nbxmike/PSOC-Console/PSOC-Creator/Composite-HID.cydsn/LEDsOut.c

/* ========================================
 *
 * Copyright 2021 Michael McCormack
 *
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
 * ========================================
*/

#include <project.h>
#include "FreeRTOS.h"
#include "timers.h"
#include "LEDsOut.h"


#define LEDSOUT_SLOW_ON           (0)
#define LEDSOUT_SLOW_OFF          (1)

#define LEDOUTPUT_ON              (1)
#define LEDOUTPUT_OFF             (0)

#define LEDSOUT_FAST_ON           (0)
#define LEDSOUT_FAST_OFF          (1)
#define LEDSOUT_DOUBLE_ONE_ON     (0)
#define LEDSOUT_DOUBLE_ONE_OFF    (1)
#define LEDSOUT_DOUBLE_TWO_ON     (2)
#define LEDSOUT_DOUBLE_TWO_OFF    (3)
#define LEDSOUT_DOUBLE_PAUSE      (4)
#define LEDSOUT_TRIPLE_ONE_ON     (0)
#define LEDSOUT_TRIPLE_ONE_OFF    (1)
#define LEDSOUT_TRIPLE_TWO_ON     (2)
#define LEDSOUT_TRIPLE_TWO_OFF    (3)
#define LEDSOUT_TRIPLE_THREE_ON   (4)
#define LEDSOUT_TRIPLE_THREE_OFF  (5)
#define LEDSOUT_TRIPLE_PAUSE      (6)
#define LEDSOUT_DASH_ON           (0)
#define LEDSOUT_DASH_OFF          (1)
#define LEDSOUT_DOT_ON            (2)
#define LEDSOUT_DOT_OFF           (3)

static LED_Output_t Leds[LEDSOUT_COUNT];
static TickType_t xLastTransactionTime;
static const uint8_t AndMasks[8] =  {0xFE, 0xFD, 0xFB, 0xF7, 0xEF, 0xDF, 0xBF, 0x7F};
static const uint8_t OrMasks[8] =  {0x01, 0x02, 0x04, 0x08, 0x10, 0x20, 0x40, 0x80};

void LEDSOut_Task(void *arg);

static int LEDsOut_Off(LED_Output_t *Led);
static int LEDsOut_SteadyOn(LED_Output_t *Led);
static int LEDsOut_Slow(LED_Output_t *Led);
static int LEDsOut_Fast(LED_Output_t *Led);
static int LEDsOut_Double(LED_Output_t *Led);
static int LEDsOut_Triple(LED_Output_t *Led);
static int LEDsOut_DashDot(LED_Output_t *Led);


int (*state_function[LEDSOUT_MODE_INVALID]) (LED_Output_t *Led) = {
    LEDsOut_Off,
    LEDsOut_SteadyOn,
    LEDsOut_Slow,
    LEDsOut_Fast,
    LEDsOut_Double,
    LEDsOut_Triple,
    LEDsOut_DashDot
};

static int LEDsOut_Off(LED_Output_t *Led)
{
    Led->onOff = LEDOUTPUT_OFF;
    return Led->onOff;
}

static int LEDsOut_SteadyOn(LED_Output_t *Led)
{
    Led->onOff = LEDOUTPUT_ON;
    return Led->onOff;
}


static int LEDsOut_Slow(LED_Output_t *Led)
{
    switch (Led->state)
    {
        case LEDSOUT_SLOW_ON:
            Led->onOff = LEDOUTPUT_ON;
            Led->count = Led->count + LEDSOUT_RATE_TICK;
            if (Led->count >= LEDSOUT_RATE_SLOW)
            {
                Led->state = LEDSOUT_SLOW_OFF;
                Led->count = 0;
            }
            break;
        case LEDSOUT_SLOW_OFF:
            Led->onOff = LEDOUTPUT_OFF;
            Led->count = Led->count + LEDSOUT_RATE_TICK;
            if (Led->count >= LEDSOUT_RATE_SLOW)
            {
                Led->state = LEDSOUT_SLOW_ON;
                Led->count = 0;
            }
            break;
        default:
            Led->state = LEDSOUT_SLOW_ON;
            break;
    }
    
    return Led->onOff;
}


static int LEDsOut_Fast(LED_Output_t *Led)
{
    switch (Led->state)
    {
        case LEDSOUT_FAST_ON:
            Led->onOff = LEDOUTPUT_ON;
            Led->count = Led->count + LEDSOUT_RATE_TICK;
            if (Led->count >= LEDSOUT_RATE_FAST)
            {
                Led->state = LEDSOUT_FAST_OFF;
                Led->count = 0;
            }
            break;
        case LEDSOUT_FAST_OFF:
            Led->onOff = LEDOUTPUT_OFF;
            Led->count = Led->count + LEDSOUT_RATE_TICK;
            if (Led->count >= LEDSOUT_RATE_FAST)
            {
                Led->state = LEDSOUT_FAST_ON;
                Led->count = 0;
            }
            break;
        default:
            Led->state = LEDSOUT_FAST_ON;
            break;
    }
    
    return Led->onOff;
}


static int LEDsOut_Double(LED_Output_t *Led)
{
    switch (Led->state)
    {
        case LEDSOUT_DOUBLE_ONE_ON:
            Led->onOff = LEDOUTPUT_ON;
            Led->count = Led->count + LEDSOUT_RATE_TICK;
            if (Led->count >= LEDSOUT_RATE_FAST)
            {
                Led->state = LEDSOUT_DOUBLE_ONE_OFF;
                Led->count = 0;
            }   
            break;
        case LEDSOUT_DOUBLE_ONE_OFF:
            Led->onOff = LEDOUTPUT_OFF;
            Led->count = Led->count + LEDSOUT_RATE_TICK;
            if (Led->count >= LEDSOUT_RATE_FAST)
            {
                Led->state = LEDSOUT_DOUBLE_TWO_ON;
                Led->count = 0;
            }   
            break;
        case LEDSOUT_DOUBLE_TWO_ON:
            Led->onOff = LEDOUTPUT_ON;
            Led->count = Led->count + LEDSOUT_RATE_TICK;
            if (Led->count >= LEDSOUT_RATE_FAST)
            {
                Led->state = LEDSOUT_DOUBLE_TWO_OFF;
                Led->count = 0;
            }   
            break;
        case LEDSOUT_DOUBLE_TWO_OFF:
            Led->onOff = LEDOUTPUT_OFF;
            Led->count = Led->count + LEDSOUT_RATE_TICK;
            if (Led->count >= LEDSOUT_RATE_FAST)
            {
                Led->state = LEDSOUT_DOUBLE_PAUSE;
                Led->count = 0;
            }
            break;
        case LEDSOUT_DOUBLE_PAUSE:
            Led->onOff = LEDOUTPUT_OFF;
            Led->count = Led->count + LEDSOUT_RATE_TICK;
            if (Led->count >= LEDSOUT_RATE_SLOW)
            {
                Led->state = LEDSOUT_DOUBLE_ONE_ON;
                Led->count = 0;
            }
            break;
        default:
            Led->state = LEDSOUT_DOUBLE_ONE_ON;
            break;
    }
    
    return Led->onOff;
}


static int LEDsOut_Triple(LED_Output_t *Led)
{
    switch (Led->state)
    {
        case LEDSOUT_TRIPLE_ONE_ON:
            Led->onOff = LEDOUTPUT_ON;
            Led->count = Led->count + LEDSOUT_RATE_TICK;
            if (Led->count >= LEDSOUT_RATE_FAST)
            {
                Led->state = LEDSOUT_TRIPLE_ONE_OFF;
                Led->count = 0;
            }
            break;
        case LEDSOUT_TRIPLE_ONE_OFF:
            Led->onOff = LEDOUTPUT_OFF;
            Led->count = Led->count + LEDSOUT_RATE_TICK;
            if (Led->count >= LEDSOUT_RATE_FAST)
            {
                Led->state = LEDSOUT_TRIPLE_TWO_ON;
                Led->count = 0;
            }
            break;
        case LEDSOUT_TRIPLE_TWO_ON:
            Led->onOff = LEDOUTPUT_ON;
            Led->count = Led->count + LEDSOUT_RATE_TICK;
            if (Led->count >= LEDSOUT_RATE_FAST)
            {
                Led->state = LEDSOUT_TRIPLE_TWO_OFF;
                Led->count = 0;
            }
            break;
        case LEDSOUT_TRIPLE_TWO_OFF:
            Led->onOff = LEDOUTPUT_OFF;
            Led->count = Led->count + LEDSOUT_RATE_TICK;
            if (Led->count >= LEDSOUT_RATE_FAST)
            {
                Led->state = LEDSOUT_TRIPLE_THREE_ON;
                Led->count = 0;
            }
            break;
        case LEDSOUT_TRIPLE_THREE_ON:
            Led->onOff = LEDOUTPUT_ON;
            Led->count = Led->count + LEDSOUT_RATE_TICK;
            if (Led->count >= LEDSOUT_RATE_FAST)
            {
                Led->state = LEDSOUT_TRIPLE_THREE_OFF;
                Led->count = 0;
            }
            break;
        case LEDSOUT_TRIPLE_THREE_OFF:
            Led->onOff = LEDOUTPUT_OFF;
            Led->count = Led->count + LEDSOUT_RATE_TICK;
            if (Led->count >= LEDSOUT_RATE_FAST)
            {
                Led->state = LEDSOUT_TRIPLE_PAUSE;
                Led->count = 0;
            }
            break;
        case LEDSOUT_TRIPLE_PAUSE:
            Led->onOff = LEDOUTPUT_OFF;
            Led->count = Led->count + LEDSOUT_RATE_TICK;
            if (Led->count >= LEDSOUT_RATE_FAST)
            {
                Led->state = LEDSOUT_TRIPLE_ONE_ON;
                Led->count = 0;
            }
            break;
        default:
            Led->state = LEDSOUT_TRIPLE_ONE_ON;
            break;
    }
    
    return Led->onOff;
}


static int LEDsOut_DashDot(LED_Output_t *Led)
{
    switch (Led->state)
    {
        case LEDSOUT_DASH_ON:
            Led->onOff = LEDOUTPUT_ON;
            Led->count = Led->count + LEDSOUT_RATE_TICK;
            if (Led->count >= LEDSOUT_RATE_SLOW)
            {
                Led->state = LEDSOUT_DASH_OFF;
                Led->count = 0;
            }
            break;
        case LEDSOUT_DASH_OFF:
            Led->onOff = LEDOUTPUT_OFF;
            Led->count = Led->count + LEDSOUT_RATE_TICK;
            if (Led->count >= LEDSOUT_RATE_FAST)
            {
                Led->state = LEDSOUT_DOT_ON;
                Led->count = 0;
            }
            break;
        case LEDSOUT_DOT_ON:
            Led->onOff = LEDOUTPUT_ON;
            Led->count = Led->count + LEDSOUT_RATE_TICK;
            if (Led->count >= LEDSOUT_RATE_FAST)
            {
                Led->state = LEDSOUT_DOT_OFF;
                Led->count = 0;
            }
            break;
        case LEDSOUT_DOT_OFF:
            Led->onOff = LEDOUTPUT_OFF;
            Led->count = Led->count + LEDSOUT_RATE_TICK;
            if (Led->count >= LEDSOUT_RATE_SLOW)
            {
                Led->state = LEDSOUT_DASH_ON;
                Led->count = 0;
            }
            break;
        default:
            Led->state = LEDSOUT_DASH_ON;
            break;
    }     
    
    return Led->onOff;
}


/**
 * @brief Intialization of the LED outputs.
 *
 * Creates the blinking task and set the outputs to defaults / known states
 *
 * @param None
 * @return None
 */
void LEDSOut_Init(void) 
{

  for (int i = 0; i < LEDSOUT_COUNT; ++i)
    {
        Leds[i].mode = LEDOUTPUT_OFF;
        Leds[i].count = 0;        
    }
  
    xTaskCreate(                  /* Create Playstation Interface task              */
        LEDSOut_Task,               /* Function implementing the task loop            */
        "LED_Out_Task",             /* String to locate the task in debugger          */
        configMINIMAL_STACK_SIZE,   /* Task's stack size (FreeTROS allocates)         */
        0,                          /* Number of parameters to pass to task  (none)   */
        3,                          /* Task's priority (medium)                       */
        0);                         /* Task handle (not used)                         */
}


/**
 * @brief Set the LED outputs mode.
 *
 * Will set an LED output to the intial state of the mode requested
 *
 * @param LEDNumber - which LED is being addressed
 * @param mode - one of the modes defined in the LEDsOut.h file
 * @return error code, 0 no error, -1 mode not defined, -2 if LEDNumber out of range.
 */
int LEDSOut_Set(unsigned int LEDNumber, unsigned int mode) 
{
    int retCode = 0;
    
    if (mode >= LEDSOUT_MODE_INVALID)
    {
        retCode = -1;
    }
    else if (LEDNumber >= LEDSOUT_COUNT)
    {
        retCode = -2;
    }
    else
    {
        Leds[LEDNumber].mode = mode;
        Leds[LEDNumber].count = 0;    
        Leds[LEDNumber].state = 0;    
        retCode = 0;
    }

  return retCode;
}



/* State machine that blinks the LEDs */
void LEDSOut_Task(void *arg) {
  int i;
  uint8_t tempOutput;
    
  (void)arg;  // Just to get rid of compiler warning . . .

  xLastTransactionTime = xTaskGetTickCount();
  
  while (1)
  {
    tempOutput = 0;
    for (i = 0; i < LEDSOUT_COUNT; ++i)
    {
        if (LEDSOUT_MODE_INVALID <= Leds[i].mode)
        {
            Leds[i].mode = LEDSOUT_OFF;
        }
        else
        {
            if (0 != (*state_function[Leds[i].mode]) (&Leds[i]))
            {
                tempOutput |= OrMasks[i];
            }
            else
            {
                tempOutput &= AndMasks[i];
            }
        }
    }
    Indicators_Write(tempOutput);
          
    vTaskDelayUntil( &xLastTransactionTime, pdMS_TO_TICKS(LEDSOUT_RATE_TICK) );
  }
}

/* [] END OF FILE */
