nbxmike/PSOC-Console/Support/PSxReceiver.py

#!/usr/bin/env python
#* coding: latin-1
#
# Copyright 2018 Michael McCormack
#
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
#  The PSx sniffer will send and entire transaction at once across the USB UART
#   it does not send byte by byte data.
#  Messages from the PSx Sniffer uses the ESC (0x1b) character to delimit fields
#   0x1b | 0x00 is the expansion of a data byte of 0x1b into encapulated data
#   0x1b | 0x01 is the start of a new transmission which has a header of elapsed time & message count
#   0x1b | 0x02 is the start of MOSI data
#   0x1b | 0x03 is the start of MISO data
#   0x1b | 0x04 is the end of message
#  Otherwise, a byte is just a data byte

import serial
import io
import sys
import select
import tty
import termios
#import time


def isdata():
  return select.select([sys.stdin], [], [], 0) == ([sys.stdin], [], [])

if len(sys.argv) < 3
  print "Usage: python PSxReceiver.py <Controller-String> <virtualUART>"
  sys.exit(0)

ControllerModel = "Unknown Controller "
SerialUART = "/dev/ttyUSB1"
if len(sys.argv) >= 2
  ControllerModel =  sys.arg[2]
if len(sys.argv) >= 3
  SerialUART =  sys.arg[3]

old_settings = termios.tcgetattr(sys.stdin)
try:
  tty.setcbreak(sys.stdin.fileno())
  with serial.Serial(SerialUART) as PSxAnalyzer
    with open(ControllerModel+"_PSx_Log.txt", "w") as PSxLog:
      PSxLog.write(ControllerModel+" PSx Controller Capture\n\r")

      c = 'A'
      while (c != '\x1b'):
        if isdata():
          c = sys.stdin.read(1)
        if PSxAnalyzer.inWaiting() > 0:
          x = ord(PSxAnalyzer.read())
          if (x == 0x1b):
             if PSxAnalyzer.inWaiting() > 0:
               x = ord(PSxAnalyzer.read())
               if (x == 0):                    # Encapulated data
                 PSxLog.write(" 0x1B")
               elif (x == 1):                    # Start of new message
                 if PSxAnalyzer.inWaiting() > 4:
                   x = ord(PSxAnalyzer.read())
                   if (x == 0x1b):
                     if (0 != ord(PSxAnalyzer.read())):
                       PSxLog.write("\n\r** Garbage Encountered\n\r")
                       continue
                   xword = x
                   x = ord(PSxAnalyzer.read())
                   if (x == 0x1b):
                     if (0 != ord(PSxAnalyzer.read())):
                       PSxLog.write("\n\r** Garbage Encountered\n\r")
                       continue
                   xword = xword + ( x << 8)
                   PSxLog.write("\n\r++ et %d" % xword)
                   if PSxAnalyzer.inWaiting() > 2:
                     x = ord(PSxAnalyzer.read())
                     if (x == 0x1b):
                       if (0 != ord(PSxAnalyzer.read())):
                         PSxLog.write("\n\r** Garbage Encountered\n\r")
                         continue
                     xword = x
                     if PSxAnalyzer.inWaiting() > 1:
                       x = ord(PSxAnalyzer.read())
                       if (x == 0x1b):
                         if PSxAnalyzer.inWaiting() > 1:
                           if (0 != ord(PSxAnalyzer.read())):
                           PSxLog.write("\n\r** Garbage Encountered\n\r")
                           continue
                         else:
                           PSxLog.write("\n\r** Garbage Encountered\n\r")
                           continue
                     xword = xword + ( x << 8)
                     PSxLog.write(", msg %d" % xword)
                   else:
                     PSxLog.write("\n\r** Garbage Encountered\n\r")
                     continue
                 else:
                   PSxLog.write("\n\r** Garbage Encountered\n\r")
                   continue

               elif (x == 2):                    # Start of PlayStation message
                 PSxLog.write(" PSx>> ")
               elif (x == 3):                    # Start of controller message
                 PSxLog.write(" Ctl>> ")
               elif (x == 4):                    # End of message
                 PSxLog.write("\n\r")
               else:
                 PSxLog.write("\n\r** Garbage Encountered\n\r")
                 continue
             else:
                 PSxLog.write("0x%X" % x)
          else:
              PSxLog.write("0x%X " % x)
      PSxLog.closed
      sys.exit(0)

finally:
    termios.tcsetattr(sys.stdin, termios.TCSADRAIN, old_settings)
